organnoise/Roulette/CAD/Shield/Shield v1/SuperSheildSketch_3.pdf

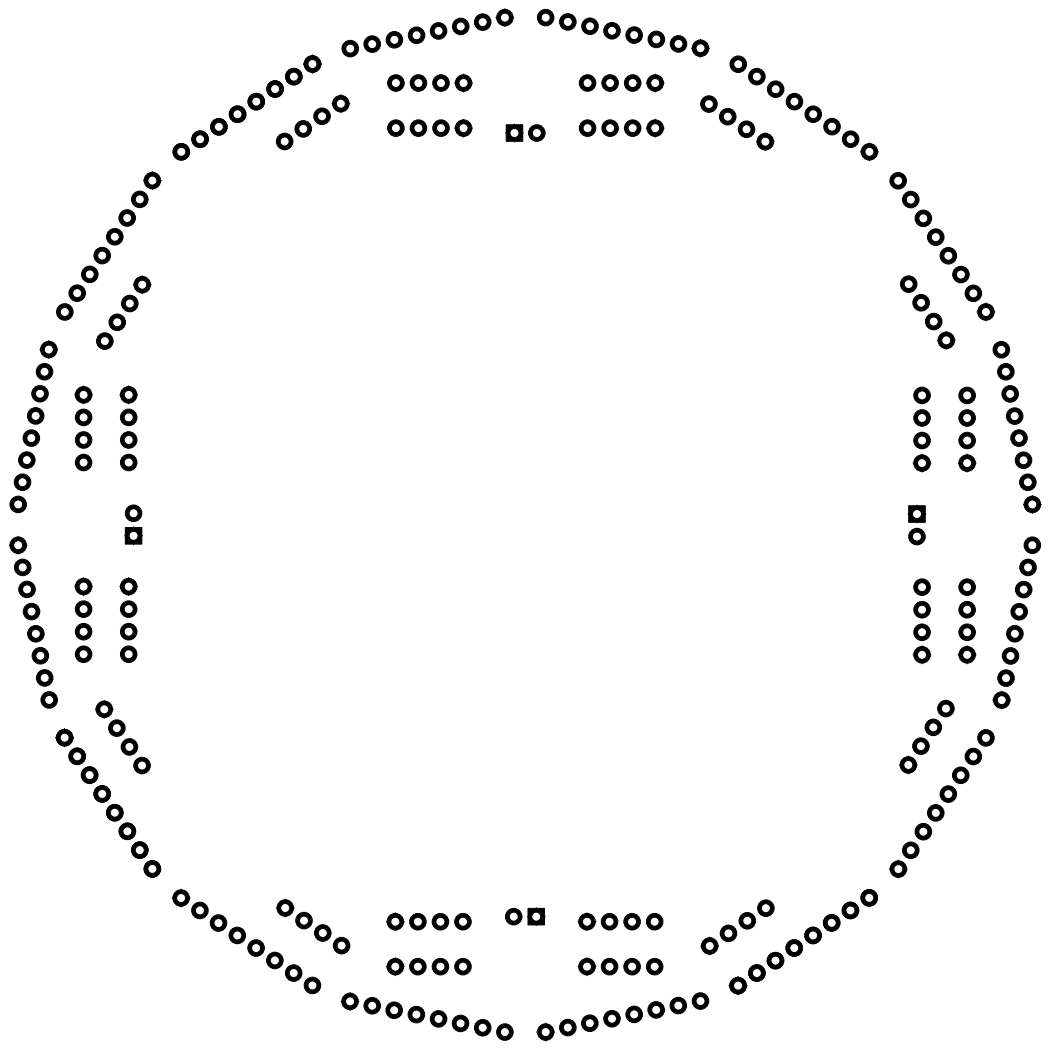
[picture p19: page 1]
