organnoise/Roulette/CAD/Paper Prototypes/Prototype_2_10.pdf

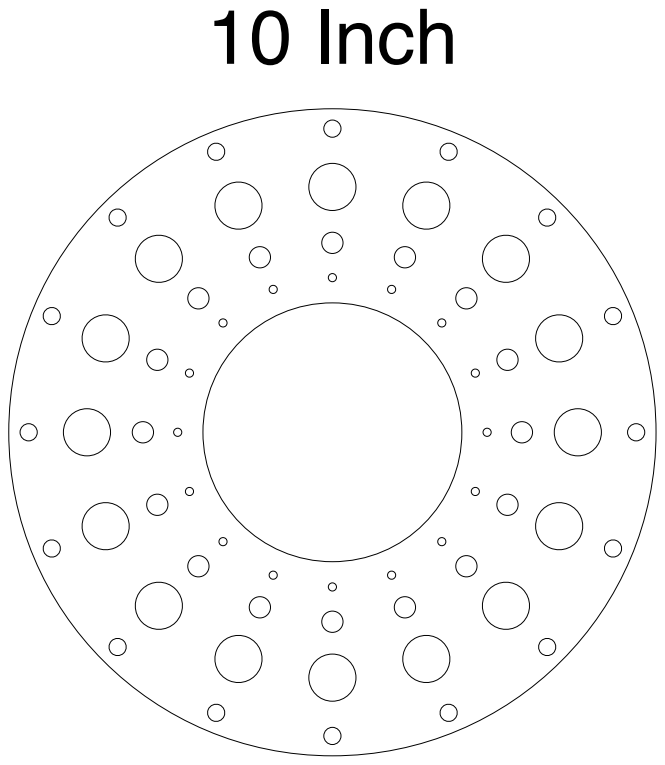
[picture p20: page 1]
10 Inch
