organnoise/Roulette/CAD/Paper Prototypes/Prototype_2_12.pdf

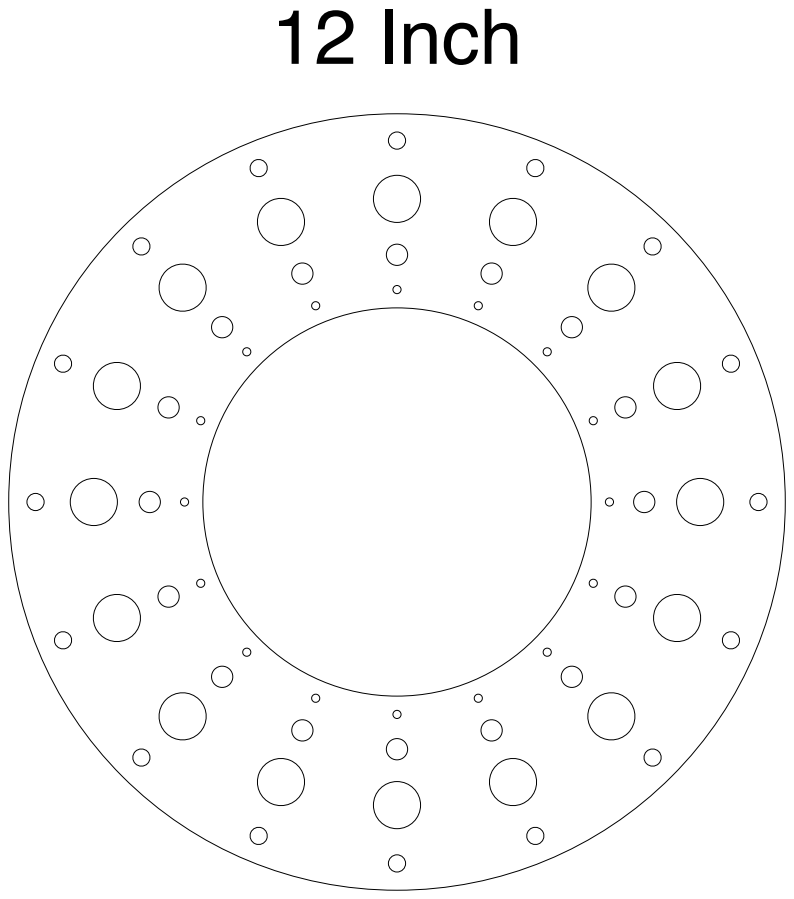
[picture p21: page 1]
12 Inch
