organnoise/Roulette/CAD/Shield/Shield v0/rouletteSheildTop_Bottom.2.pdf

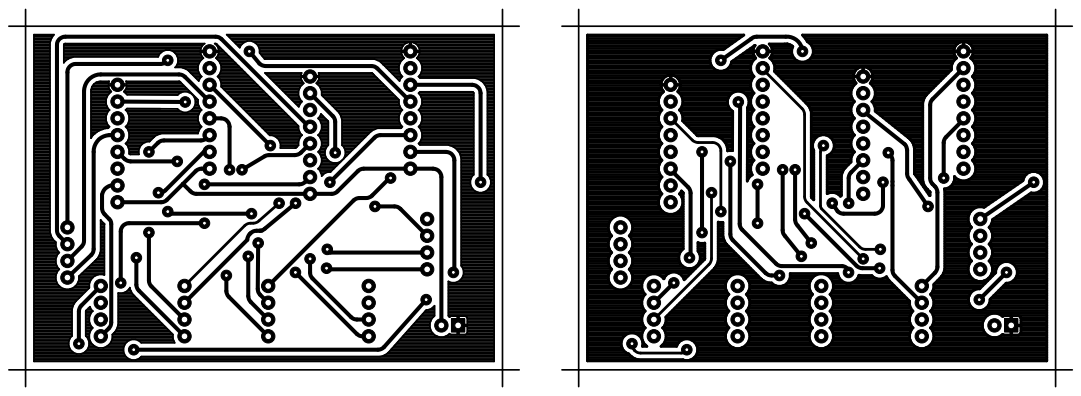
[picture p22: page 1]
