organnoise/Roulette/CAD/Shield/Shield v0/rouletteSheildTop_Bottom.pdf

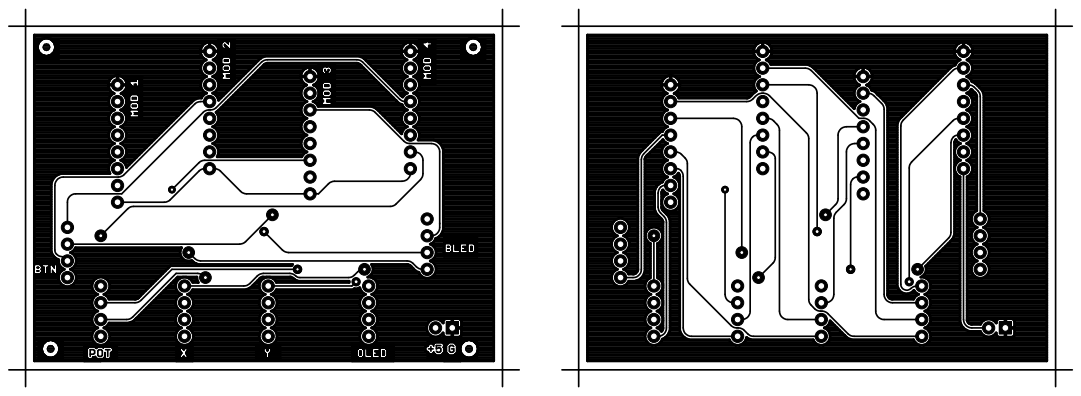
[picture p23: page 1]
