organnoise/Roulette/CAD/Shield/Shield v0/rouletteSheildTop_Bottomx2.2.pdf

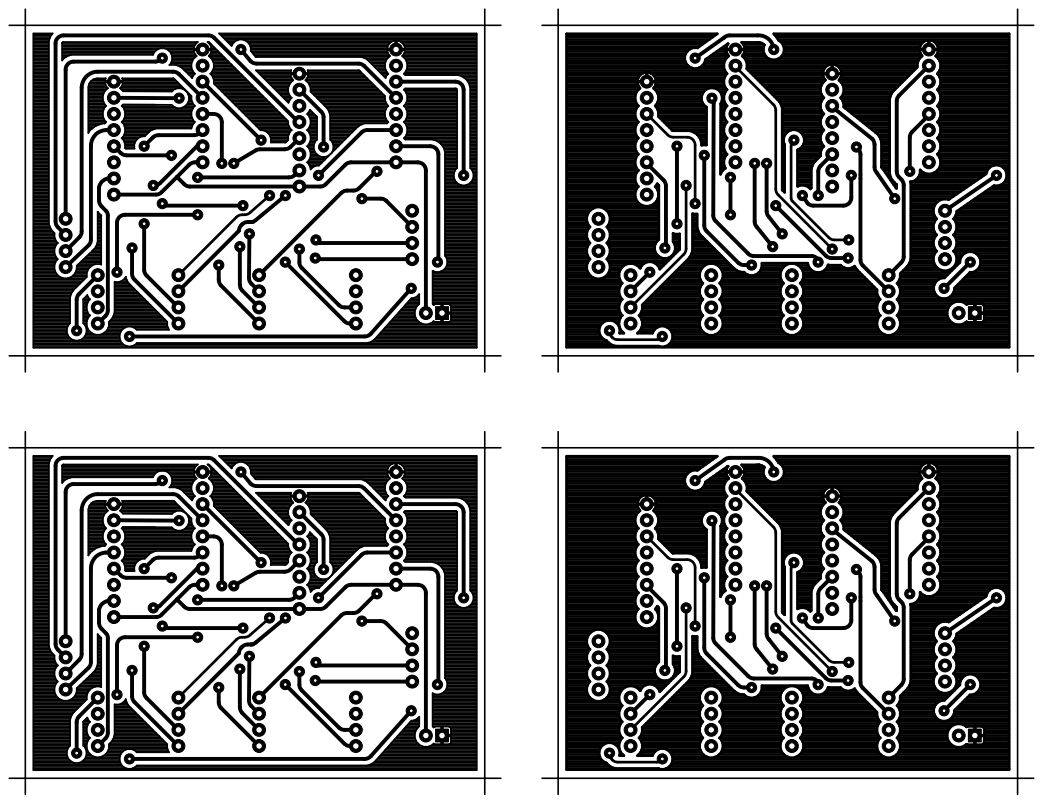
[picture p24: page 1]
