organnoise/Roulette/CAD/Shield/Shield v0/rouletteSheildTop_Bottomx2.pdf

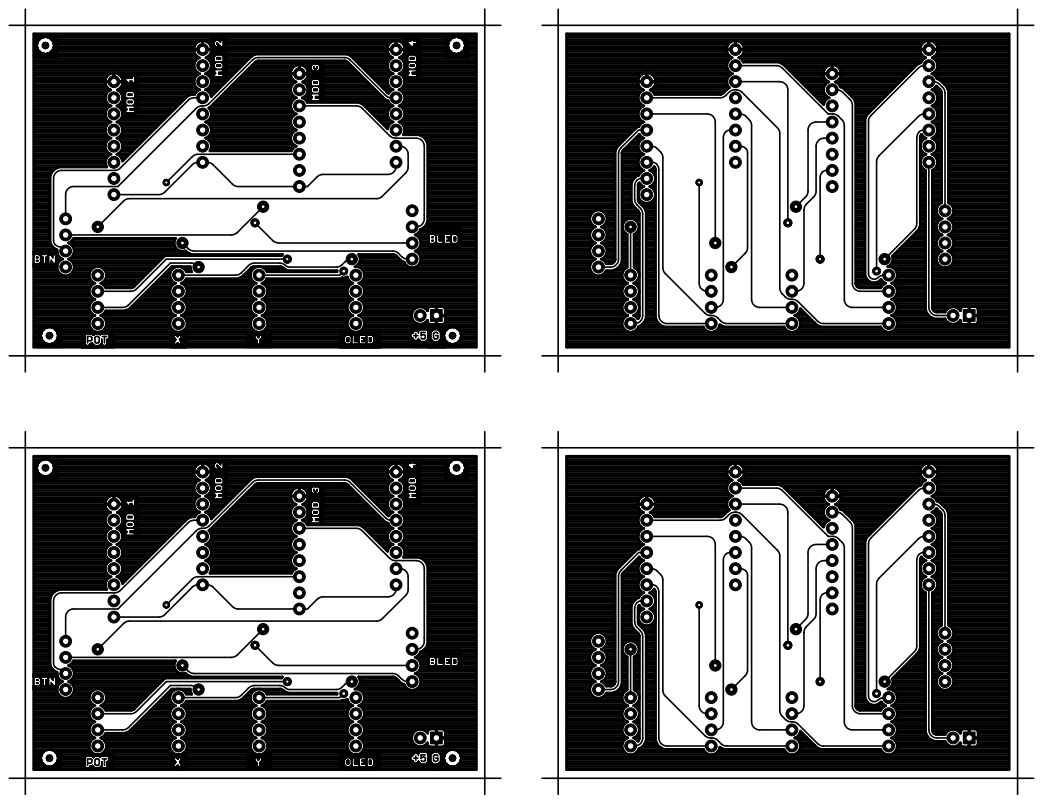
[picture p25: page 1]
