organnoise/Roulette/CAD/Shield/Shield v0/rouletteSheildTop_Bottomx4.pdf

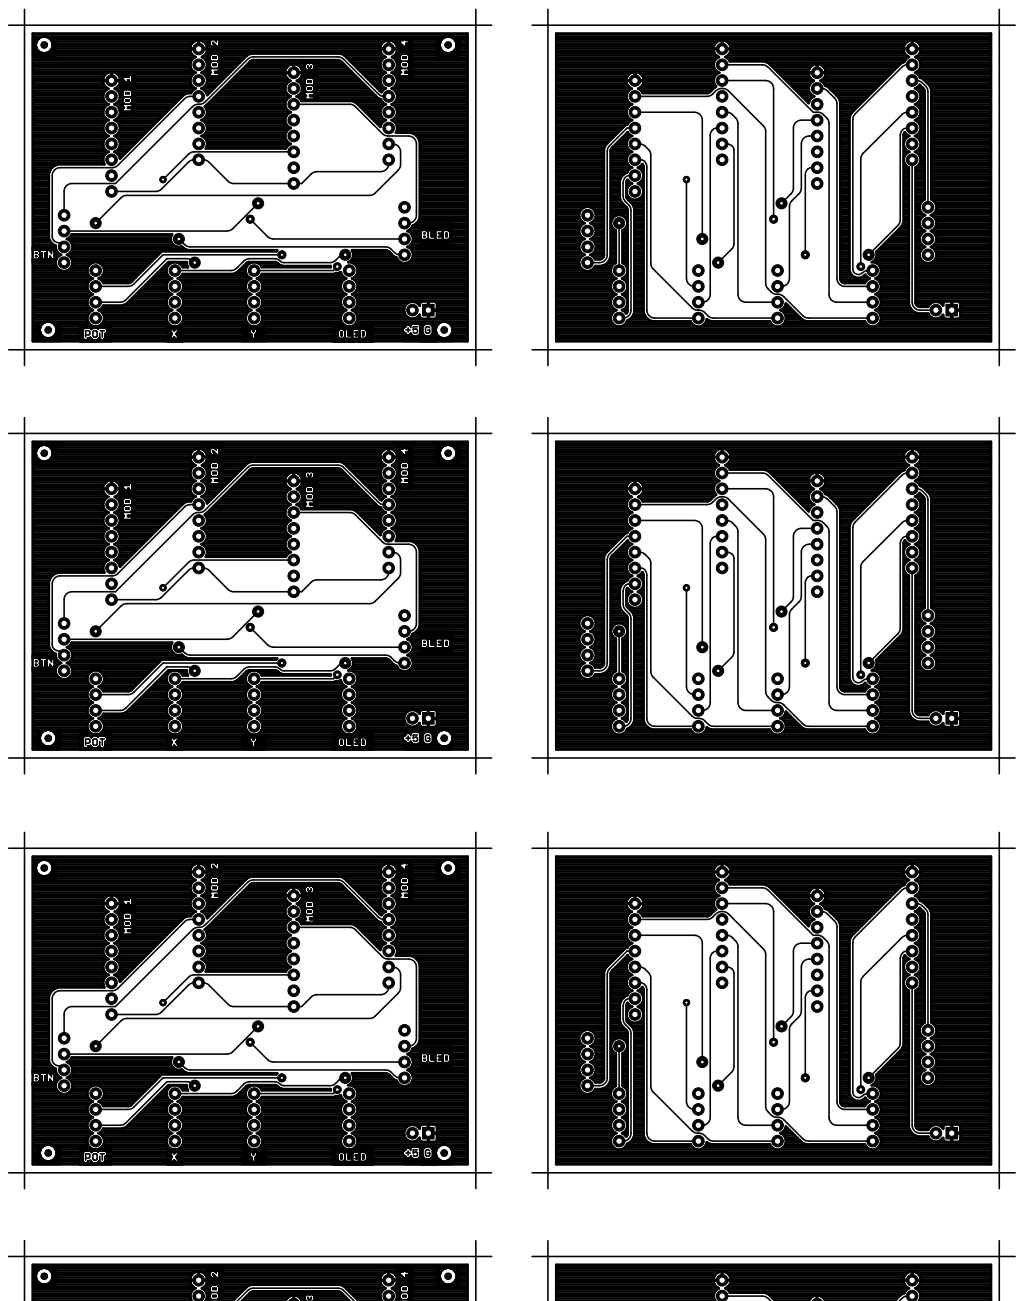
[picture p26: page 1]

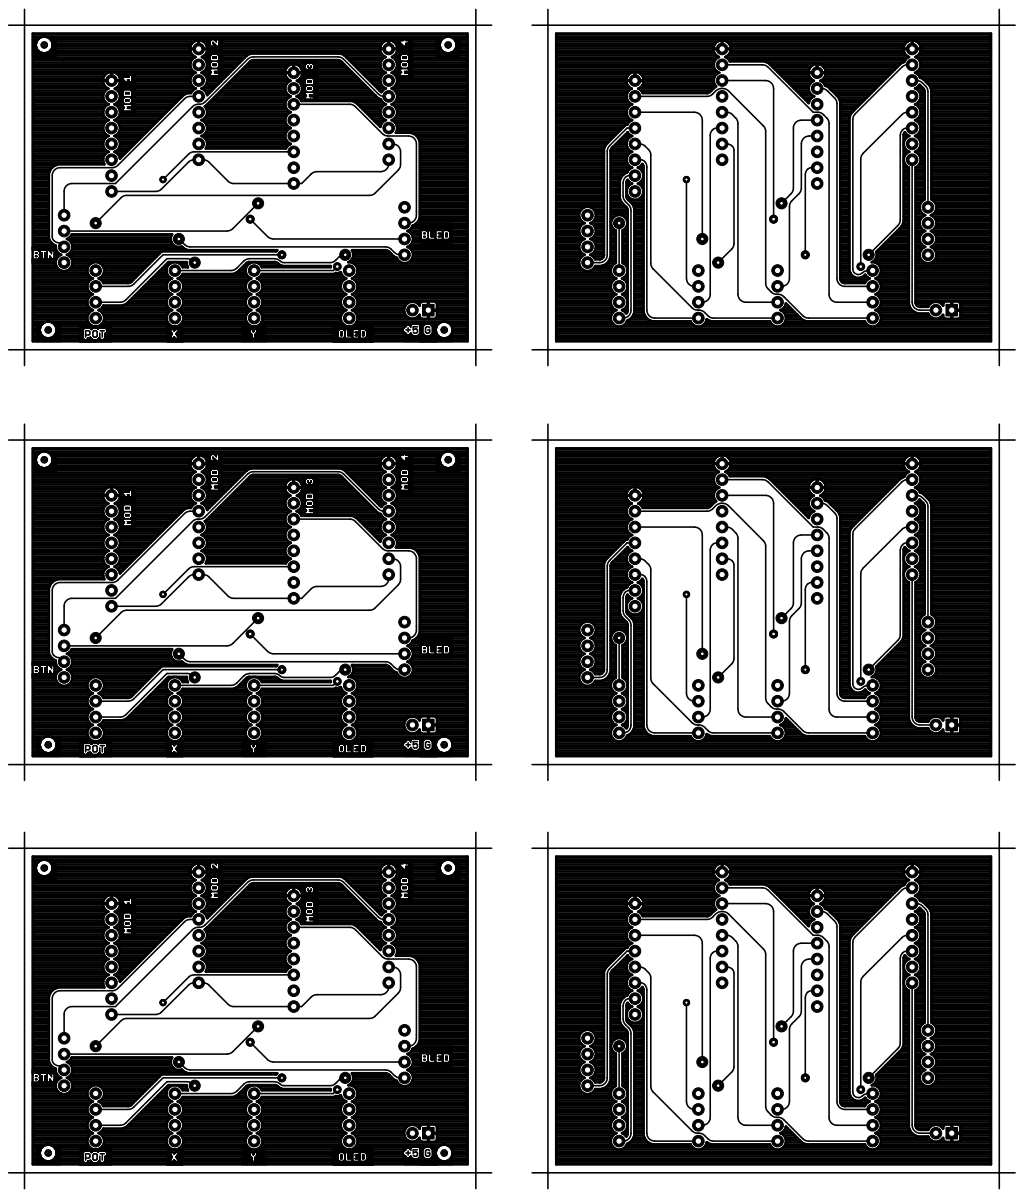
[picture p27: page 2]

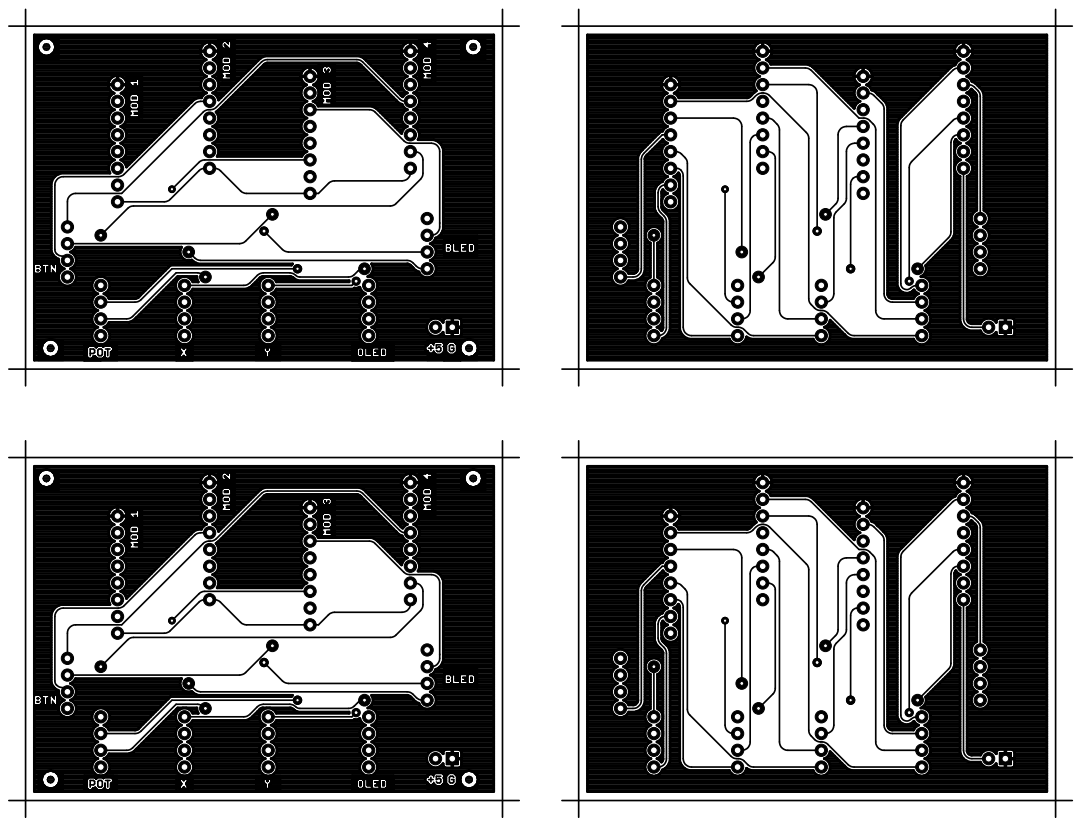
[picture p28: page 3]
