organnoise/Roulette/CAD/Shield/Shield v0/rouletteShield4.3_bottom.pdf

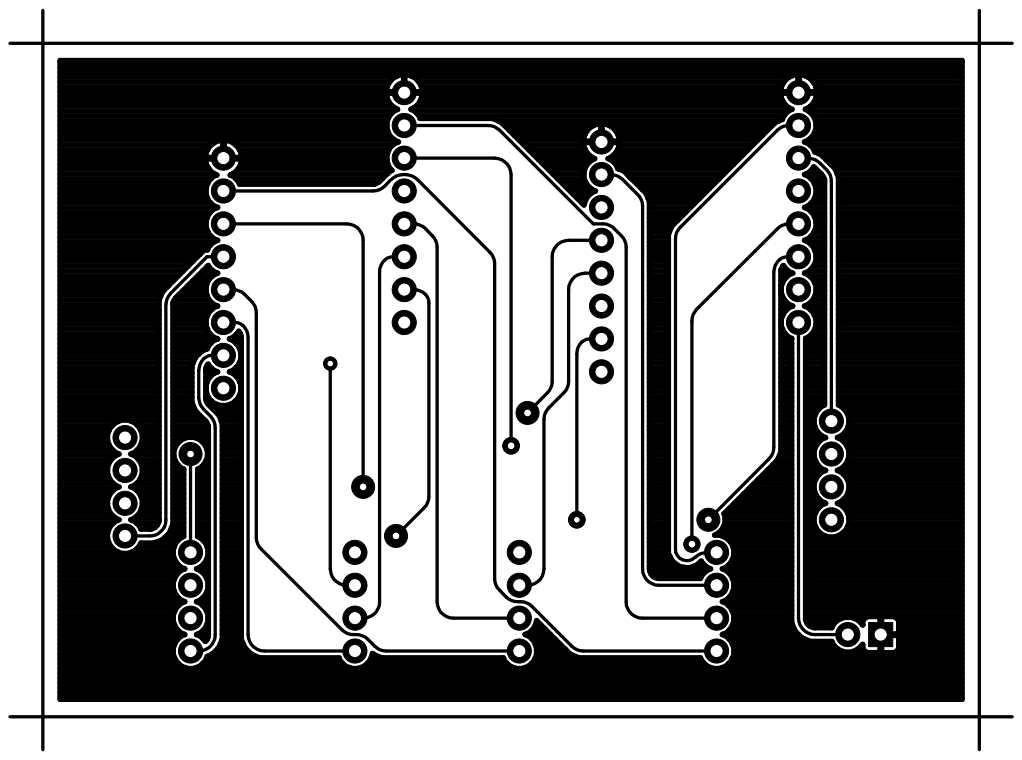
[picture p29: page 1]
