organnoise/Roulette/CAD/Shield/Shield v0/rouletteShield4.3_top.pdf

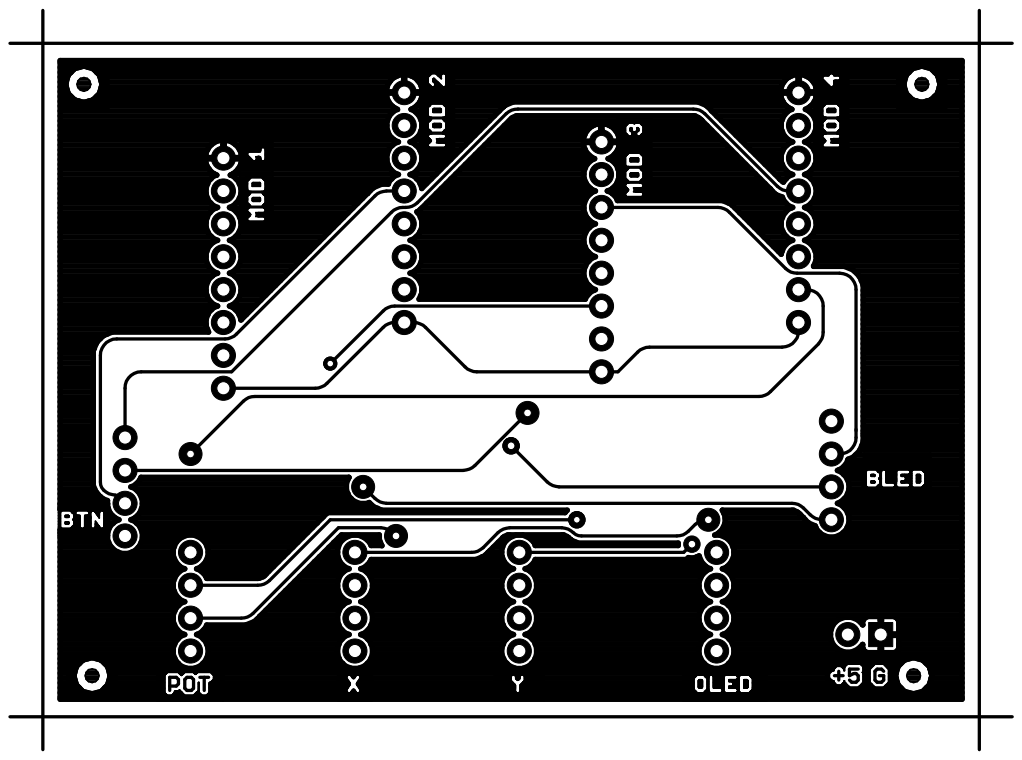
[picture p30: page 1]
