organnoise/Roulette/CAD/Shield/Shield v0/rouletteShield4.5_bottom.pdf

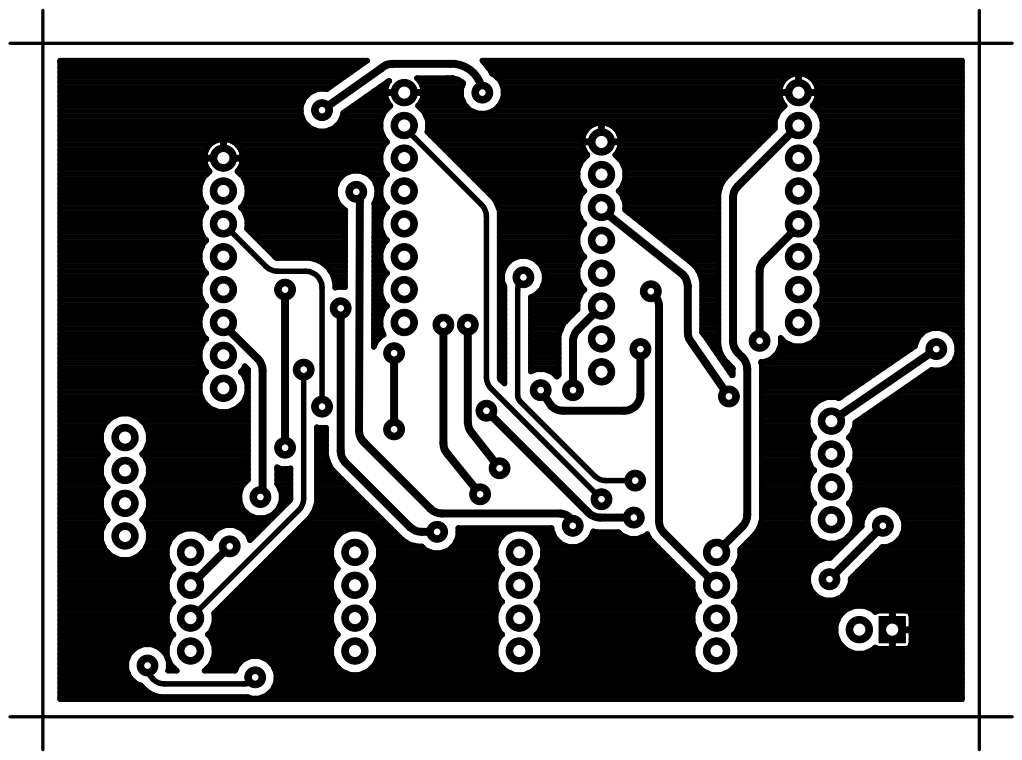
[picture p31: page 1]
