organnoise/Roulette/CAD/Shield/Shield v0/rouletteShield4.5_top.pdf

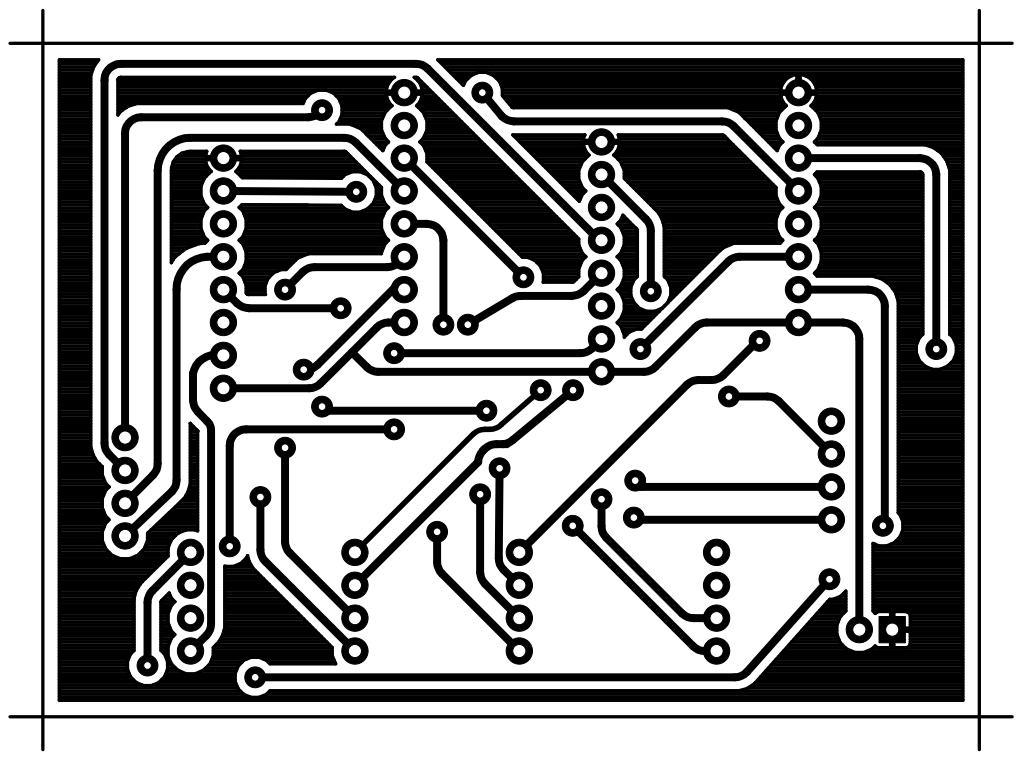
[picture p32: page 1]
